xaio6/6-axis-manipulator/docs/2.jpg

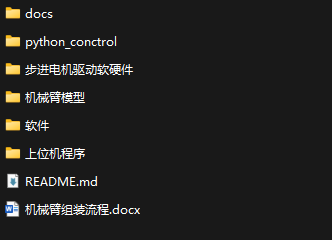
docs/2.jpg
