xaio6/6-axis-manipulator/Arm_Model/GT2_5_20齿.SLDPRT

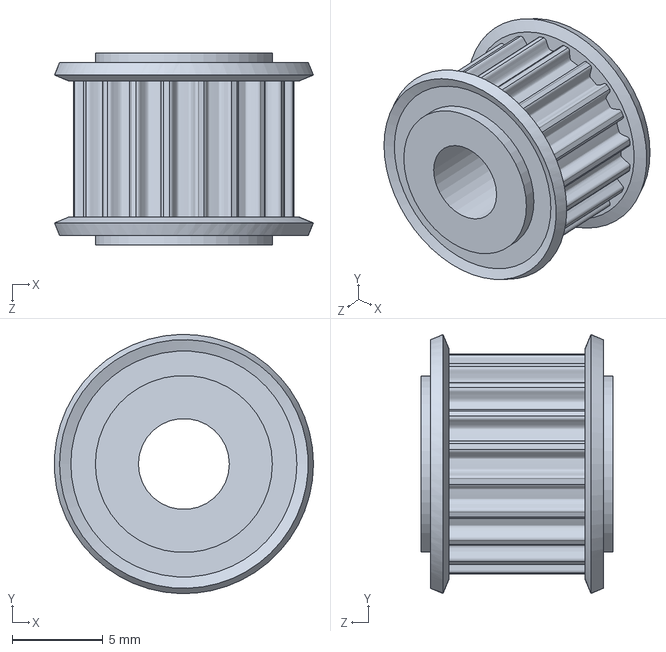
[picture p58: CAD file, 2025-11-28]
Arm_Model/GT2_5_20齿.SLDPRT
14.2 x 14.2 x 10.5 mm
