xaio6/6-axis-manipulator/Arm_Model/Arm 2.3.SLDPRT

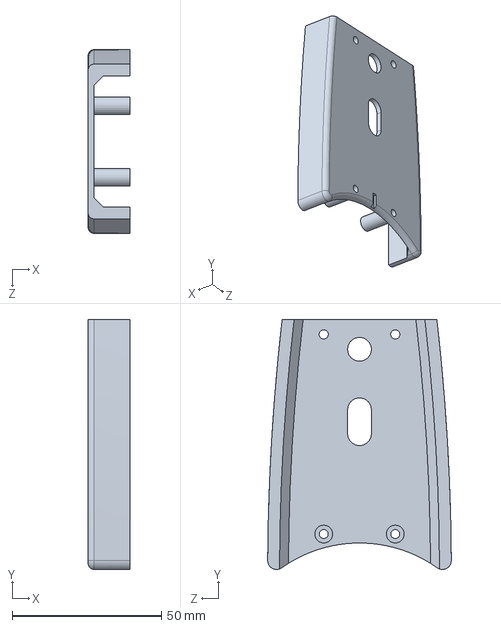
[picture p59: CAD file, 2025-11-28]
Arm_Model/Arm 2.3.SLDPRT
14.0 x 83.9 x 61.6 mm
