xaio6/6-axis-manipulator/Arm_Model/Baseplate.SLDPRT

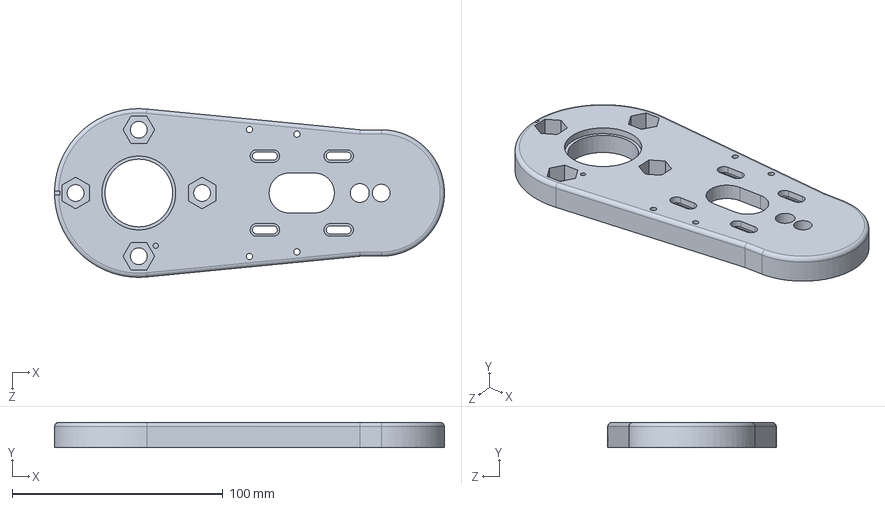
[picture p60: CAD file, 2025-11-28]
Arm_Model/Baseplate.SLDPRT
185.0 x 12.0 x 80.0 mm
