xaio6/6-axis-manipulator/Arm_Model/Bottom support.SLDPRT

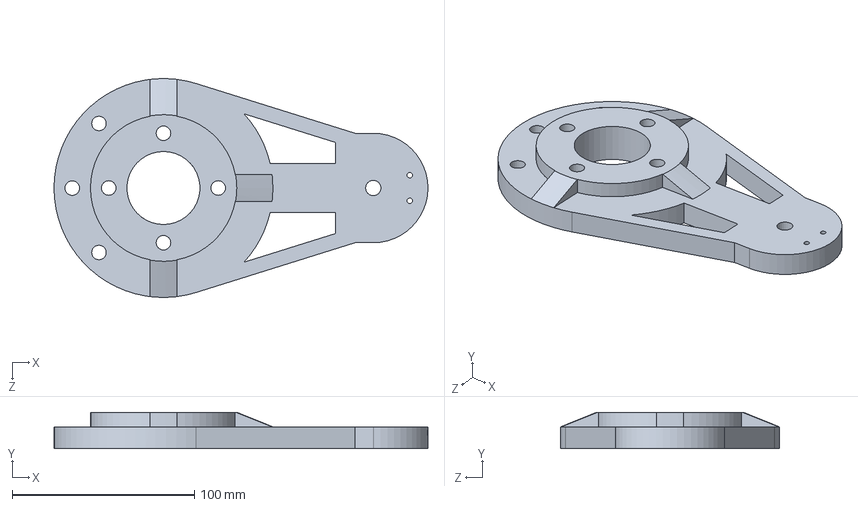
[picture p61: CAD file, 2025-11-28]
Arm_Model/Bottom support.SLDPRT
205.0 x 20.0 x 120.0 mm
