xaio6/6-axis-manipulator/Arm_Model/Motor3 spacer .SLDPRT

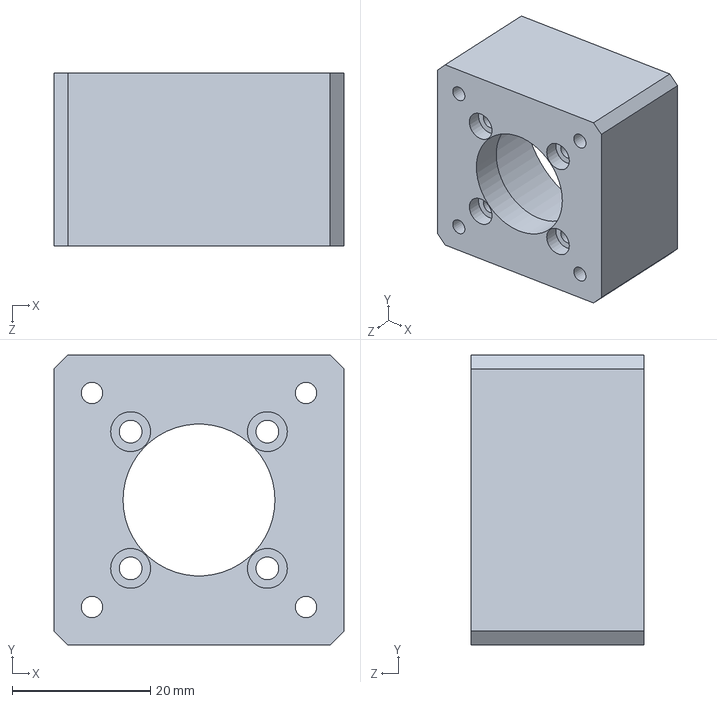
[picture p62: CAD file, 2025-11-28]
Arm_Model/Motor3 spacer .SLDPRT
42.0 x 42.0 x 25.0 mm
