xaio6/6-axis-manipulator/Arm_Model/Pulley100Tv5.SLDPRT

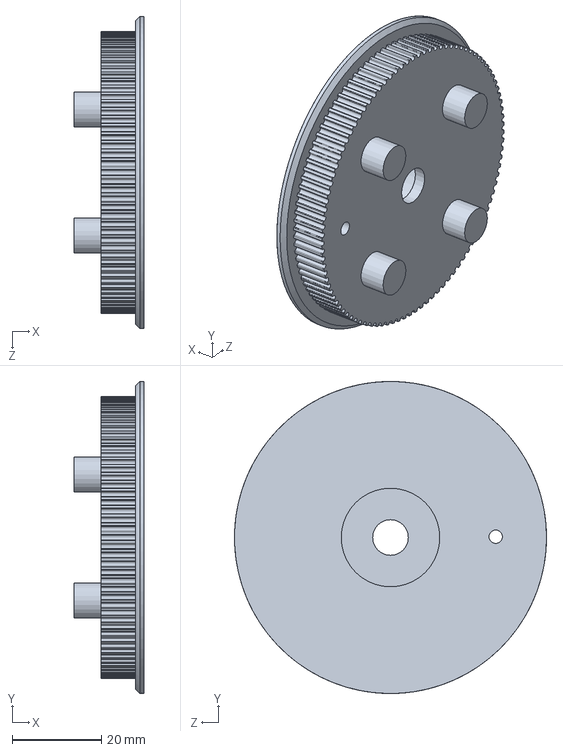
[picture p63: CAD file, 2025-11-28]
Arm_Model/Pulley100Tv5.SLDPRT
15.6 x 70.0 x 70.0 mm
