xaio6/6-axis-manipulator/Arm_Model/Motor1 spacer.SLDPRT

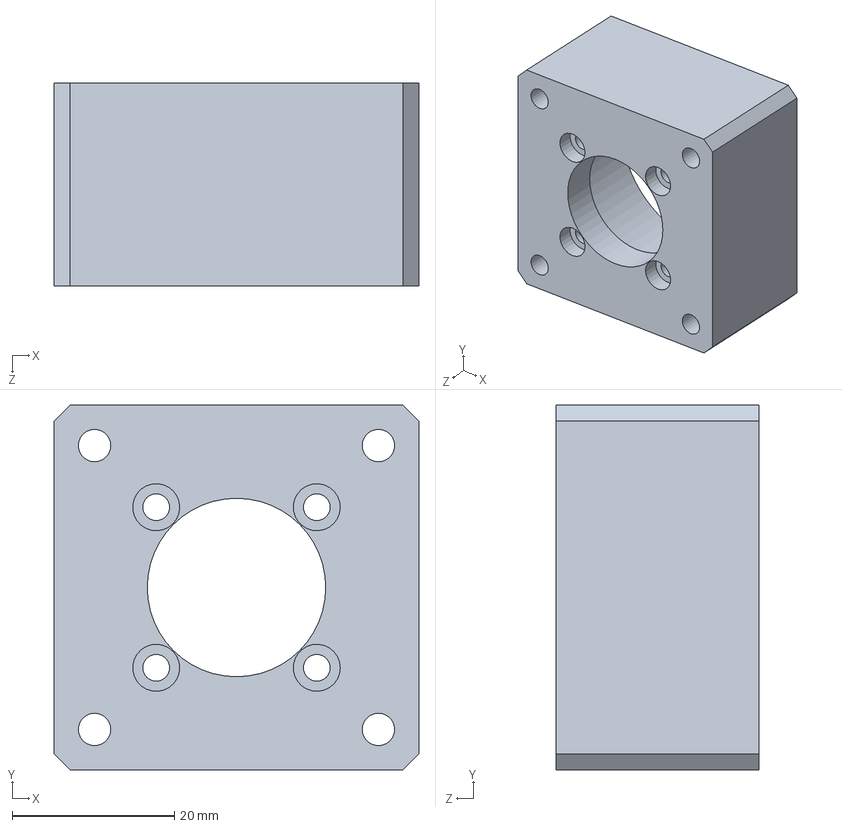
[picture p64: CAD file, 2025-11-28]
Arm_Model/Motor1 spacer.SLDPRT
45.0 x 45.0 x 25.0 mm
