xaio6/6-axis-manipulator/Arm_Model/6轴配件.SLDPRT

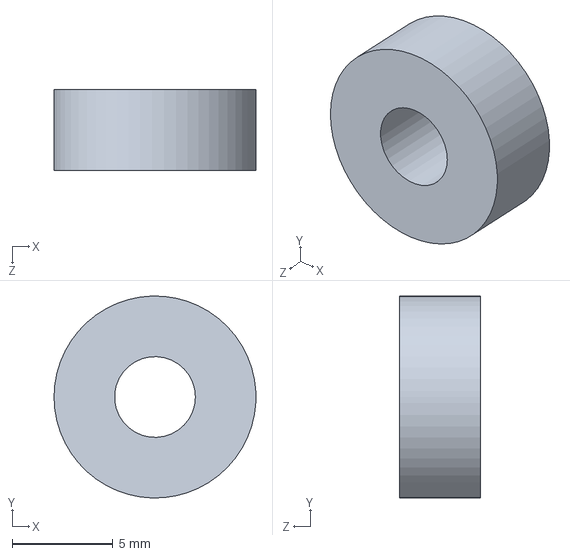
[picture p65: CAD file, 2025-11-28]
Arm_Model/6轴配件.SLDPRT
10.00 x 10.00 x 4.00 mm
