xaio6/6-axis-manipulator/Arm_Model/15mm 1.6 rikka.SLDPRT

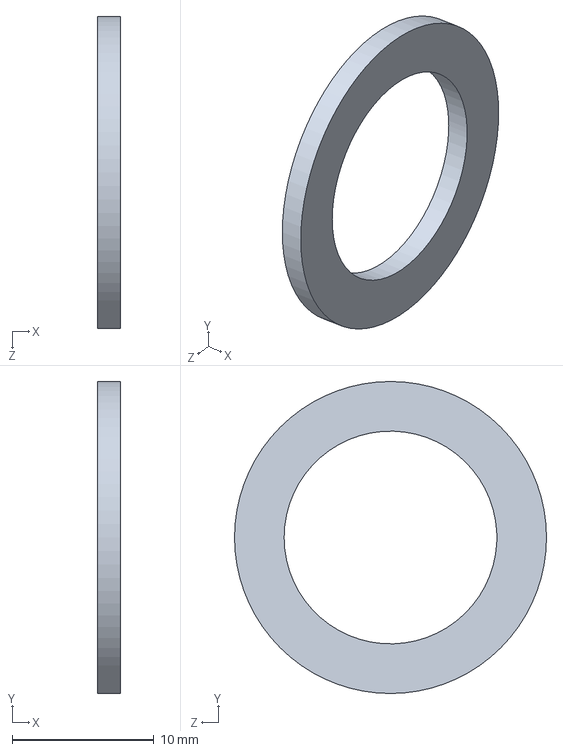
[picture p66: CAD file, 2025-11-28]
Arm_Model/15mm 1.6 rikka.SLDPRT
1.60 x 22.0 x 22.0 mm
