xaio6/6-axis-manipulator/Arm_Model/Basewall cover v2.SLDPRT

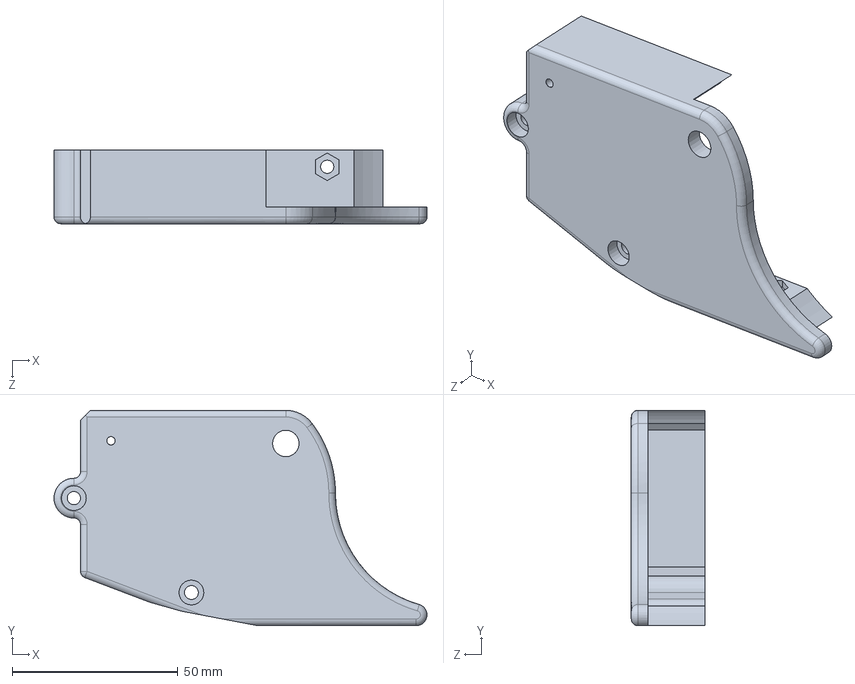
[picture p67: CAD file, 2025-11-28]
Arm_Model/Basewall cover v2.SLDPRT
112.6 x 65.0 x 22.2 mm
