xaio6/6-axis-manipulator/Arm_Model/15mm rikka 1.2mm.SLDPRT

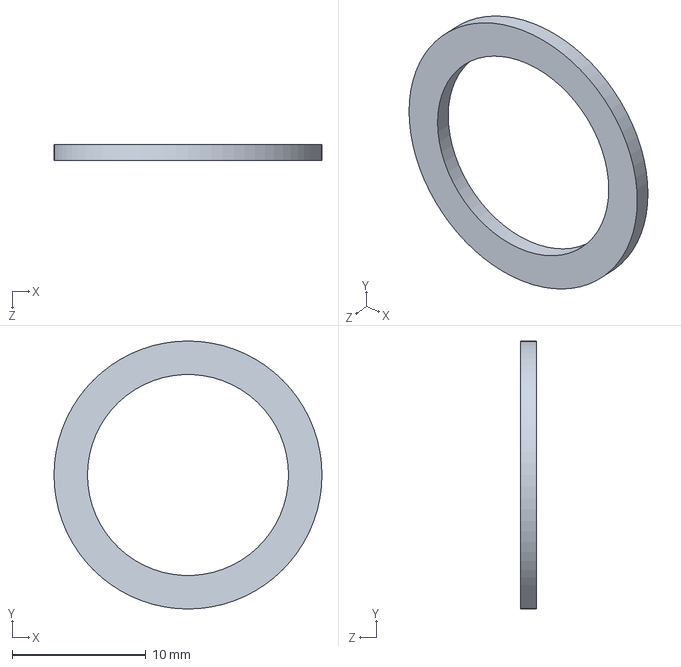
[picture p68: CAD file, 2025-11-28]
Arm_Model/15mm rikka 1.2mm.SLDPRT
20.0 x 20.0 x 1.20 mm
