xaio6/6-axis-manipulator/Arm_Model/3M HTD 16T 6mm Bore.SLDPRT

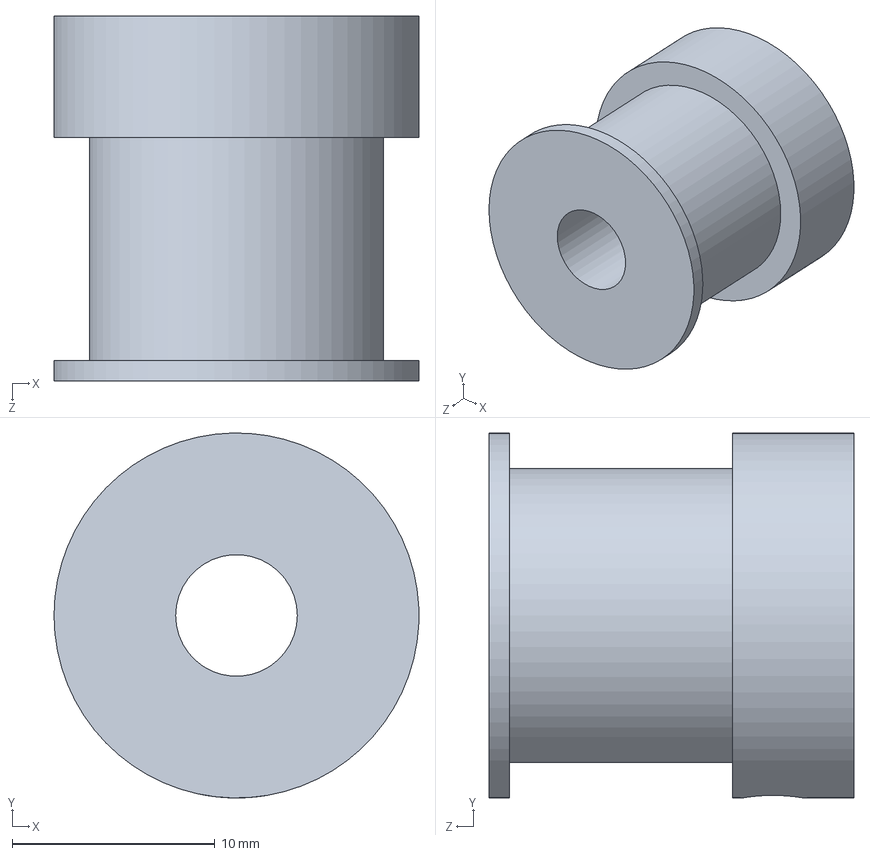
[picture p69: CAD file, 2025-11-28]
Arm_Model/3M HTD 16T 6mm Bore.SLDPRT
18.0 x 18.0 x 18.0 mm
