xaio6/6-axis-manipulator/Arm_Model/Toothless pulley 16t gt2.SLDPRT

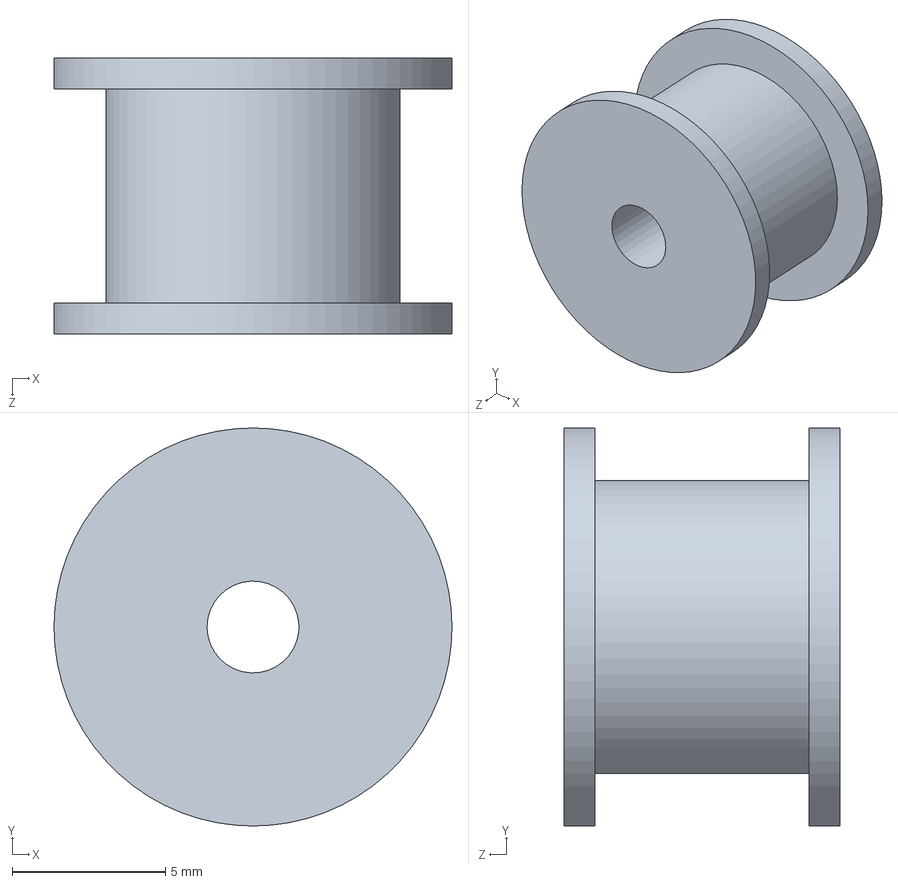
[picture p70: CAD file, 2025-11-28]
Arm_Model/Toothless pulley 16t gt2.SLDPRT
13.0 x 13.0 x 9.00 mm
