xaio6/6-axis-manipulator/Arm_Model/Pulley32TGT2.SLDPRT

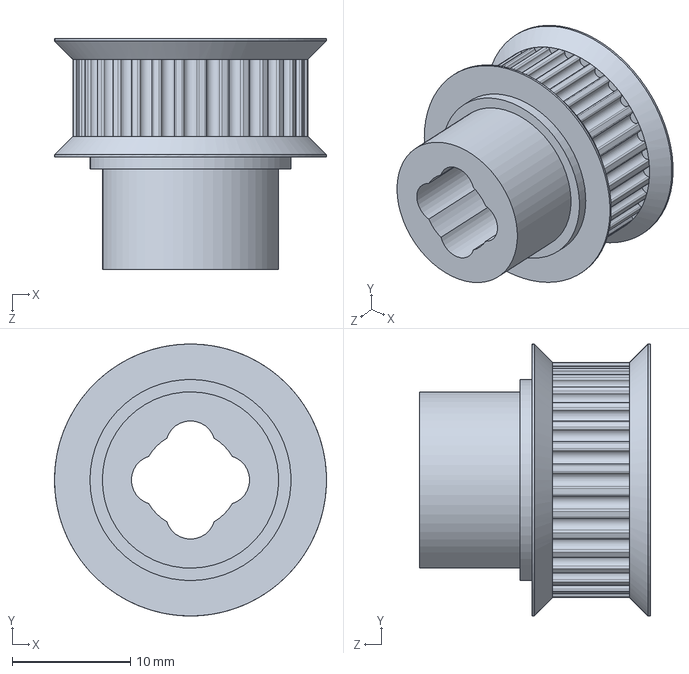
[picture p71: CAD file, 2025-11-28]
Arm_Model/Pulley32TGT2.SLDPRT
23.0 x 23.0 x 19.5 mm
