xaio6/6-axis-manipulator/Arm_Model/BaseWall_2_v2.SLDPRT

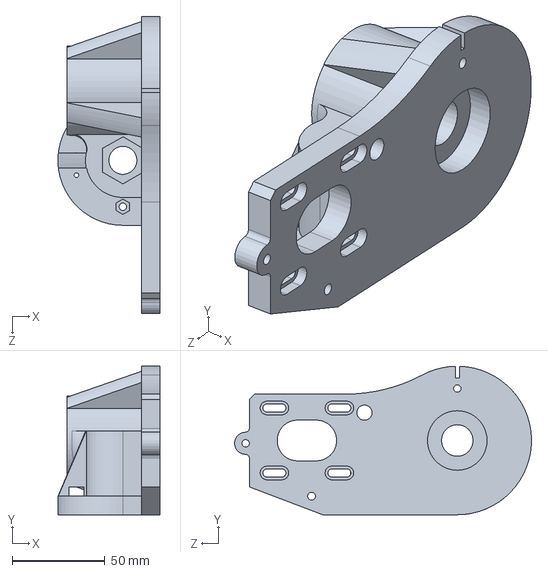
[picture p72: CAD file, 2025-11-28]
Arm_Model/BaseWall_2_v2.SLDPRT
54.9 x 80.0 x 160.0 mm
