xaio6/6-axis-manipulator/Arm_Model/Nema 17 planetary 5 to 1 gearbox.SLDPRT

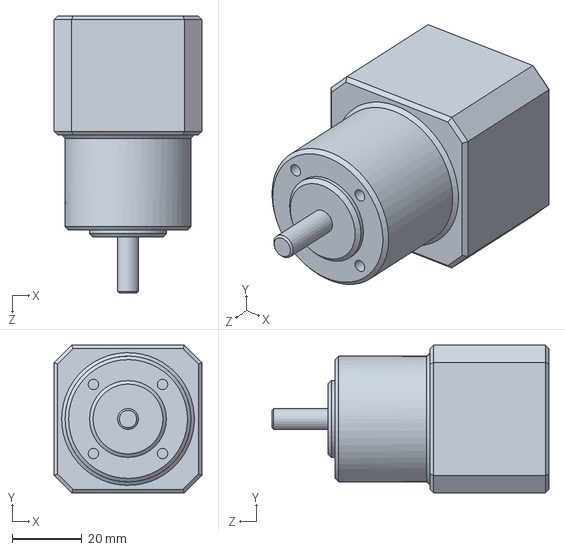
[picture p73: CAD file, 2025-11-28]
Arm_Model/Nema 17 planetary 5 to 1 gearbox.SLDPRT
42.3 x 42.3 x 79.3 mm
