xaio6/6-axis-manipulator/Arm_Model/Arm2Mountv2.SLDPRT

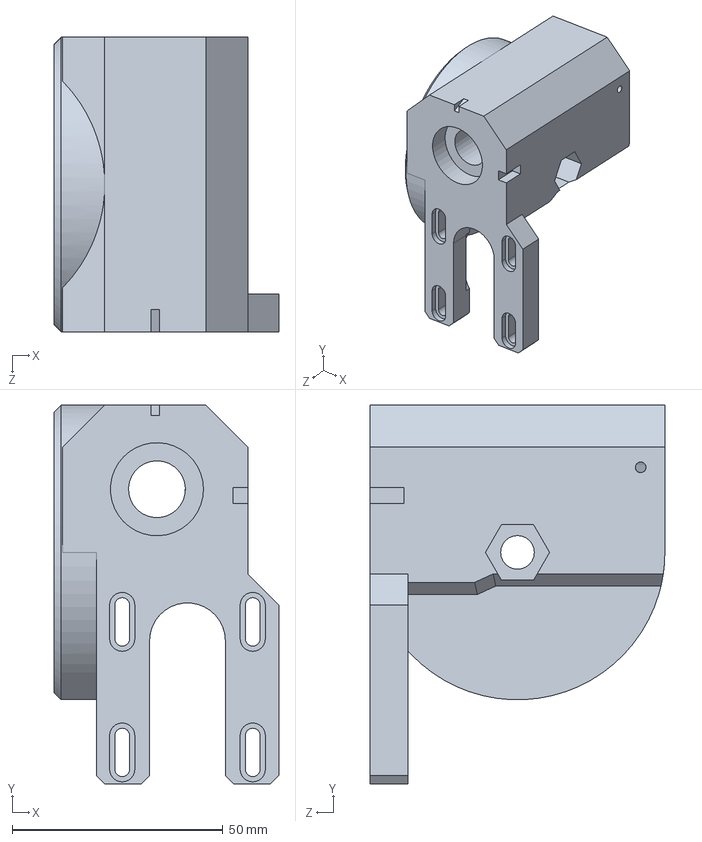
[picture p74: CAD file, 2025-11-28]
Arm_Model/Arm2Mountv2.SLDPRT
53.3 x 90.0 x 70.0 mm
