xaio6/6-axis-manipulator/Arm_Model/42_J6_kotelo_1.SLDPRT

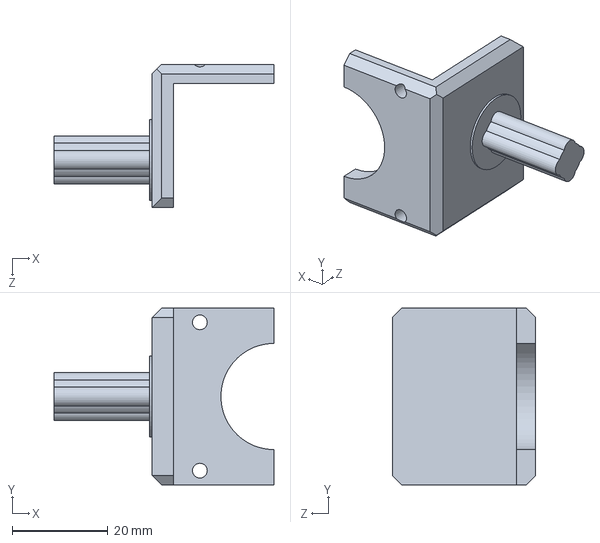
[picture p75: CAD file, 2025-11-28]
Arm_Model/42_J6_kotelo_1.SLDPRT
46.0 x 37.0 x 30.0 mm
