xaio6/6-axis-manipulator/Arm_Model/Arm1v2.SLDPRT

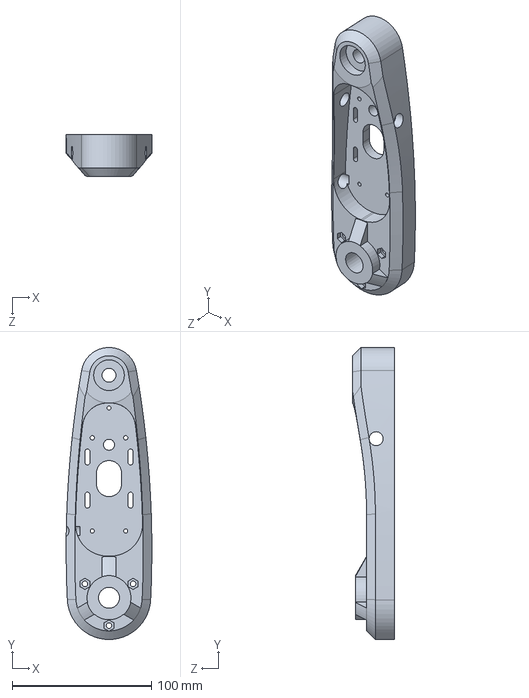
[picture p76: CAD file, 2025-11-28]
Arm_Model/Arm1v2.SLDPRT
61.6 x 209.9 x 30.0 mm
