xaio6/6-axis-manipulator/Arm_Model/Pulley100TBase.SLDPRT

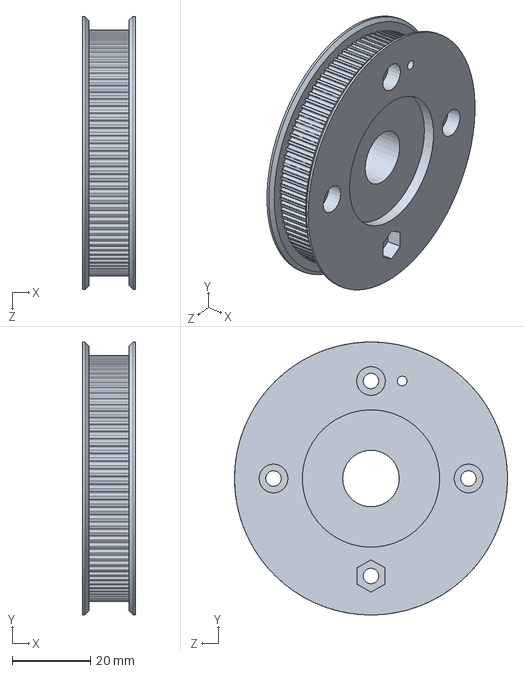
[picture p77: CAD file, 2025-11-28]
Arm_Model/Pulley100TBase.SLDPRT
13.5 x 70.0 x 70.0 mm
