xaio6/6-axis-manipulator/Arm_Model/Nema8 Stepperi (banggood.com).SLDPRT

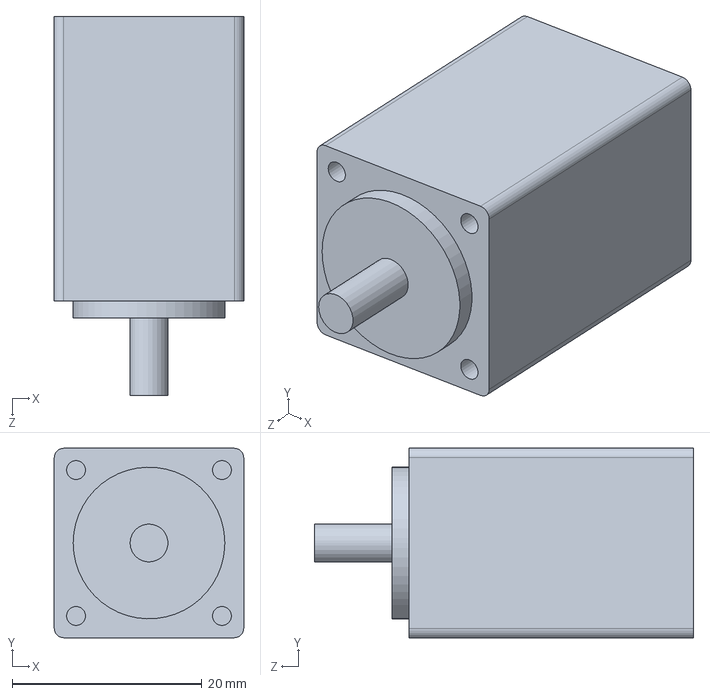
[picture p78: CAD file, 2025-11-28]
Arm_Model/Nema8 Stepperi (banggood.com).SLDPRT
20.0 x 20.0 x 40.0 mm
