xaio6/6-axis-manipulator/Arm_Model/42_J6_kotelo_2.SLDPRT

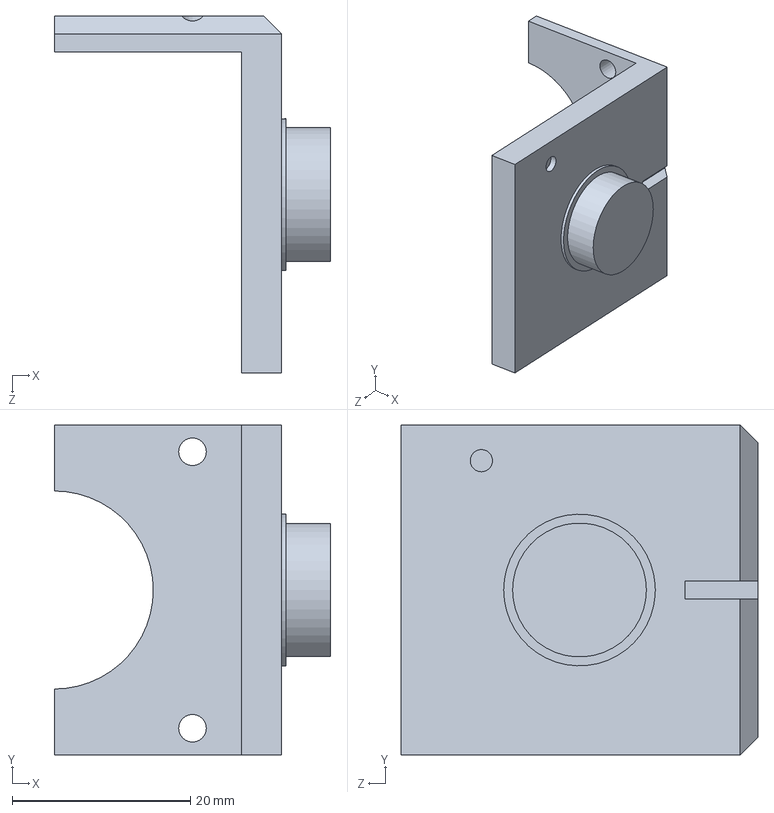
[picture p79: CAD file, 2025-11-28]
Arm_Model/42_J6_kotelo_2.SLDPRT
31.0 x 37.0 x 40.0 mm
