xaio6/6-axis-manipulator/Arm_Model/Bottom Tube.SLDPRT

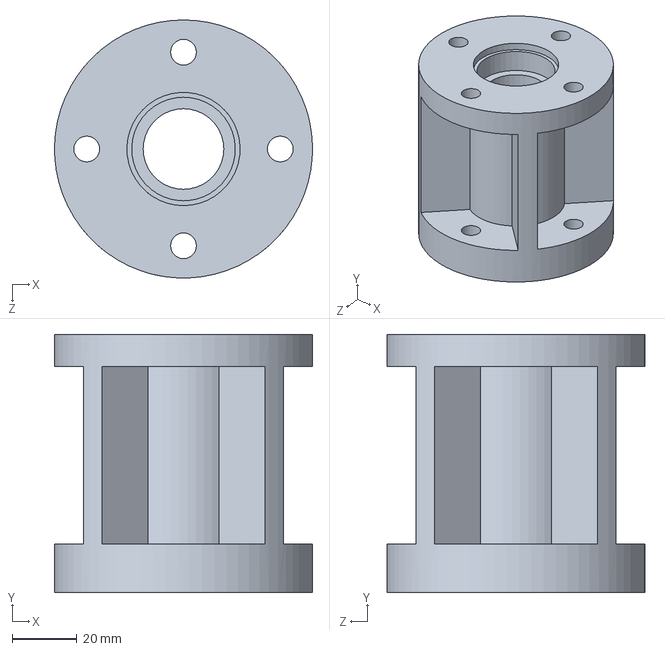
[picture p80: CAD file, 2025-11-28]
Arm_Model/Bottom Tube.SLDPRT
80.0 x 80.0 x 80.0 mm
