xaio6/6-axis-manipulator/Arm_Model/M14.SLDPRT

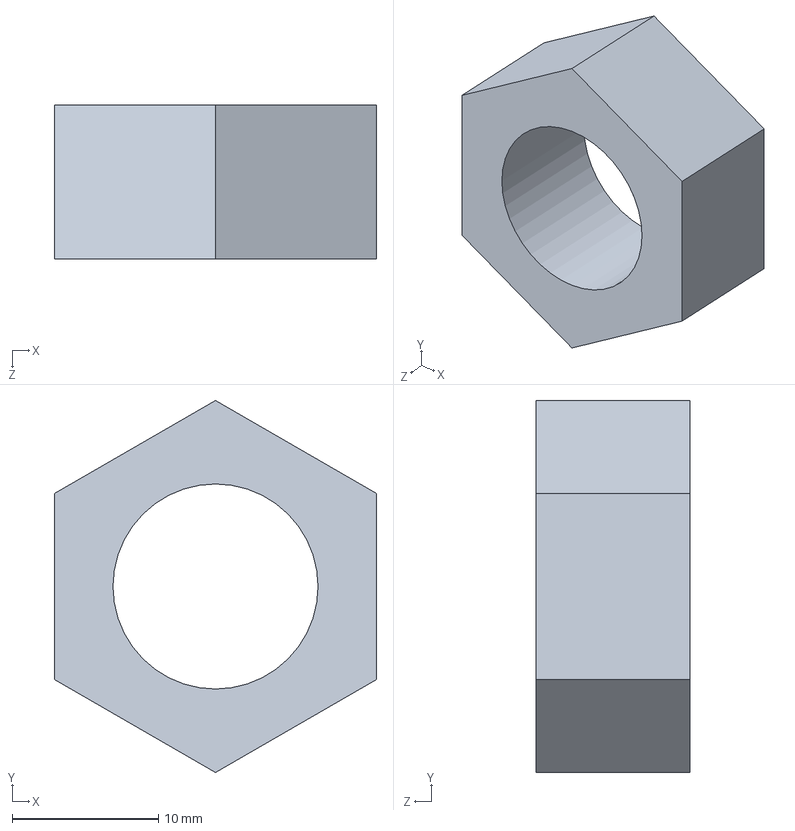
[picture p81: CAD file, 2025-11-28]
Arm_Model/M14.SLDPRT
22.0 x 25.4 x 10.5 mm
