xaio6/6-axis-manipulator/Arm_Model/42末端Pulley60Tv2.SLDPRT

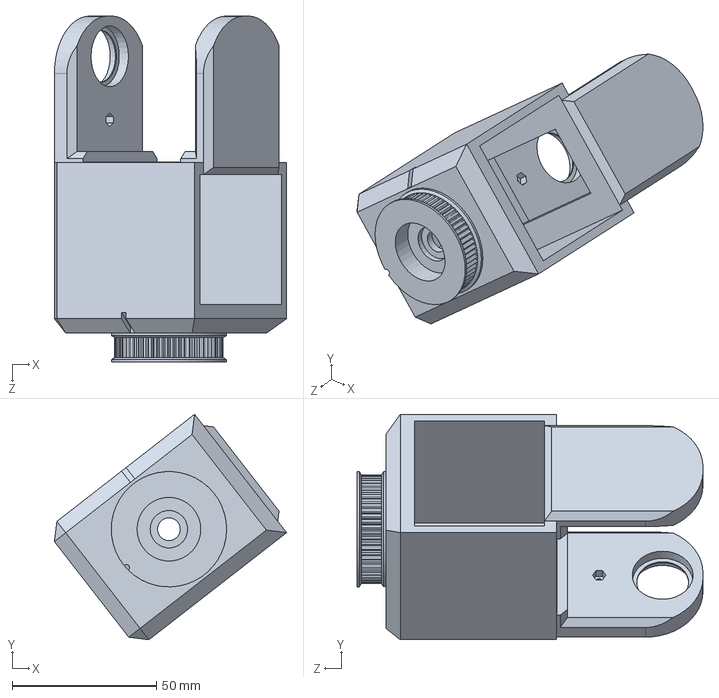
[picture p82: CAD file, 2025-11-28]
Arm_Model/42末端Pulley60Tv2.SLDPRT
80.6 x 78.2 x 120.0 mm
