xaio6/6-axis-manipulator/Arm_Model/Assem4_v2.SLDASM

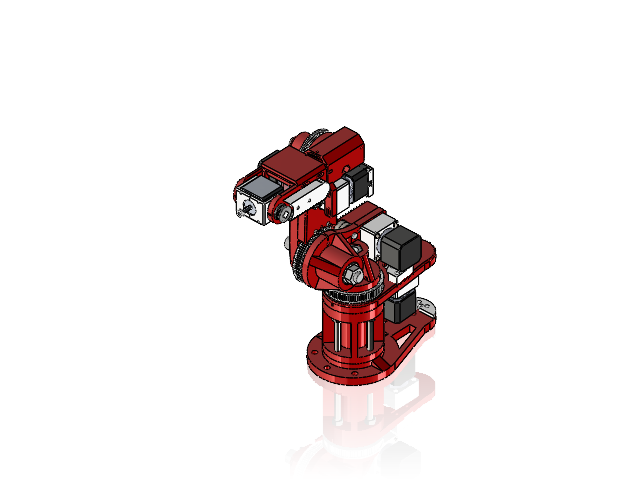
[picture p83: CAD file, 2025-11-28]
Arm_Model/Assem4_v2.SLDASM
hex nut style 1 gradeab_iso x 23
Arm2Mountv2
HTD3M 80T
plain washer normal grade a_iso x 8
Arm 2.3
angular contact ball bearing_68_iso x 12
socket head cap screw_iso x 27
GT2_16T_13x14
Arm1v2
M14-110mm
Nema 17 planetary 5 to 1 gearbox x 5
Motor3 spacer x 3
3M HTD 16T 6mm Bore x 2
Basewall cover v2
M8-40mm - Copy
BaseWall_2_v2
M14 x 2
Motor1 spacer x 2
M14-150mm
thrust ball bearing_68_iso x 2
Baseplate
Bottom Tube
Bottom support
6轴配件
电机后盖 x 2
42末端Pulley60Tv2
Pulley32TGT2
垫片 x 2
GT2_5_20齿 x 2
Pulley100Tv5
42_J6_kotelo_2
42末端同步轮盖子
压线盖
压同步轮带盖
Toothless pulley 16t gt2 x 2
压同步轮带盖2
HTD3M 80T_base
Nema 14 stepper
42_J6_kotelo_1
